FKMTime/firmware/src/state.rs

use crate::consts::NVS_SAVED_STATE;
use crate::{
    structs::{BleDisplayDevice, PossibleGroup},
    utils::error_log::ErrorLogEntry,
    utils::signaled_mutex::SignaledMutex,
};
use alloc::{rc::Rc, string::String, vec::Vec};
use embassy_sync::{
    blocking_mutex::raw::{CriticalSectionRawMutex, NoopRawMutex},
    mutex::Mutex,
    signal::Signal,
};
use embassy_time::{Duration, Instant, Timer};
use esp_hal::aes::Aes;
use esp_hal_wifimanager::Nvs;
use serde::{Deserialize, Serialize};

pub static mut SIGN_KEY: u32 = 0;
pub static mut TRUST_SERVER: bool = false;
pub static mut FKM_TOKEN: i32 = 0;
pub static mut SECURE_RFID: bool = false;
pub static mut AUTO_SETUP: bool = false;

pub static mut GROUP_LIMIT: Option<u64> = None;

pub static mut EPOCH_BASE: u64 = 0;
pub static mut SLEEP_STATE: bool = false;
pub static mut DEEPER_SLEEP: bool = false;
pub static mut OTA_STATE: bool = false;

#[cfg(feature = "v4")]
pub static mut BUZZER_VOLUME: u8 = crate::consts::BUZZER_VOLUME_DEFAULT;

#[cfg(feature = "v4")]
#[inline(always)]
pub fn buzzer_volume() -> u8 {
    unsafe { BUZZER_VOLUME }
}

#[cfg(feature = "v4")]
#[inline(always)]
pub fn set_buzzer_volume(volume: u8) {
    unsafe {
        BUZZER_VOLUME = volume;
    }
}

#[inline(always)]
pub fn current_epoch() -> u64 {
    unsafe { EPOCH_BASE + Instant::now().as_secs() }
}

#[inline(always)]
pub fn sleep_state() -> bool {
    unsafe { SLEEP_STATE }
}

#[inline(always)]
pub fn deeper_sleep_state() -> bool {
    unsafe { DEEPER_SLEEP }
}

#[inline(always)]
pub fn ota_state() -> bool {
    unsafe { OTA_STATE }
}

#[derive(Debug, PartialEq, Clone)]
#[allow(dead_code)]
pub enum Scene {
    Update,

    /// Waiting for wifi connection
    WifiConnect,

    /// Connect to wifi to setup
    AutoSetupWait,

    /// Waiting for MDNS
    MdnsWait,

    WaitingForCompetitor,
    GroupSelect,
    CompetitorInfo,
    Inspection,
    Timer,
    Finished,
}

#[derive(Debug, PartialEq, Clone)]
pub enum MenuScene {
    Signing,
    Unsigning,
    BtDisplay,
    ErrorLog,
    #[cfg(feature = "v4")]
    BuzzerVolume,
}

#[derive(Debug, PartialEq, Clone)]
pub enum ErrorLogEntryStage {
    #[cfg(feature = "v4")]
    Qr,
    // Shared stage used on both variants for post-selection detail view.
    Details,
}

impl Scene {
    pub fn can_be_lcd_overwritten(&self) -> bool {
        match self {
            Scene::Update => false,
            Scene::WifiConnect => false,
            Scene::AutoSetupWait => false,
            Scene::MdnsWait => false,
            Scene::WaitingForCompetitor => true,
            Scene::GroupSelect => true,
            Scene::CompetitorInfo => true,
            Scene::Inspection => false,
            Scene::Timer => false,
            Scene::Finished => false,
        }
    }

    pub fn to_index(&self) -> usize {
        match self {
            Scene::Update => 0,
            Scene::WifiConnect => 1,
            Scene::AutoSetupWait => 2,
            Scene::MdnsWait => 3,
            Scene::WaitingForCompetitor => 4,
            Scene::GroupSelect => 5,
            Scene::CompetitorInfo => 6,
            Scene::Inspection => 7,
            Scene::Timer => 8,
            Scene::Finished => 9,
        }
    }

    pub fn can_sleep(&self) -> bool {
        !matches!(
            self,
            Scene::Update | Scene::WifiConnect | Scene::AutoSetupWait
        )
    }
}

impl PartialOrd for Scene {
    fn partial_cmp(&self, other: &Self) -> Option<core::cmp::Ordering> {
        Some(self.to_index().cmp(&other.to_index()))
    }
}

#[cfg(feature = "e2e")]
#[derive(Default)]
pub struct End2End {
    pub buttons_sig: Signal<CriticalSectionRawMutex, (usize, u64)>,
    pub card_scan_sig: Signal<CriticalSectionRawMutex, u128>,
    pub stackmat_sig:
        Signal<CriticalSectionRawMutex, (crate::utils::stackmat::StackmatTimerState, u64)>,
}

#[cfg(feature = "e2e")]
impl End2End {
    pub fn new() -> Self {
        End2End {
            ..Default::default()
        }
    }
}

#[derive(Debug, Clone, PartialEq)]
pub enum BleAction {
    Connect(BleDisplayDevice),
    StartScan,
    Unpair,
}

pub type GlobalState = Rc<GlobalStateInner>;
pub struct GlobalStateInner {
    pub state: SignaledMutex<CriticalSectionRawMutex, SignaledGlobalStateInner>,
    pub timer_signal: Signal<NoopRawMutex, u64>,
    pub timer_stop_signal: Signal<NoopRawMutex, ()>,
    pub bt_display_signal: Signal<NoopRawMutex, u64>,
    pub update_progress: Signal<CriticalSectionRawMutex, u8>,
    pub sign_unsign_progress: Signal<CriticalSectionRawMutex, bool>,
    pub ble_sig: Signal<CriticalSectionRawMutex, BleAction>,
    pub show_battery: Signal<CriticalSectionRawMutex, u8>,
    #[cfg(feature = "v4")]
    pub buzzer_sound_test: Signal<CriticalSectionRawMutex, ()>,

    pub nvs: Nvs,
    pub aes: Mutex<NoopRawMutex, Aes<'static>>,

    #[cfg(feature = "e2e")]
    pub e2e: End2End,
}

impl GlobalStateInner {
    pub fn new(nvs: &Nvs, aes: esp_hal::peripherals::AES<'static>) -> Self {
        Self {
            state: SignaledMutex::new(SignaledGlobalStateInner::new()),
            timer_signal: Signal::new(),
            timer_stop_signal: Signal::new(),
            bt_display_signal: Signal::new(),
            update_progress: Signal::new(),
            sign_unsign_progress: Signal::new(),
            ble_sig: Signal::new(),
            show_battery: Signal::new(),
            #[cfg(feature = "v4")]
            buzzer_sound_test: Signal::new(),

            nvs: nvs.clone(),
            aes: Mutex::new(Aes::new(aes)),

            #[cfg(feature = "e2e")]
            e2e: End2End::new(),
        }
    }
}

#[derive(Debug, Clone)]
pub struct SignaledGlobalStateInner {
    pub scene: Scene,
    pub menu_scene: Option<MenuScene>,

    pub inspection_start: Option<Instant>,
    pub inspection_end: Option<Instant>,
    pub solve_time: Option<u64>,
    pub penalty: Option<i8>,
    pub session_id: Option<String>,
    pub time_confirmed: bool,
    pub solve_group: Option<PossibleGroup>,

    pub error_text: Option<String>,

    pub possible_groups: Vec<PossibleGroup>,
    pub group_selected_idx: usize,

    pub selected_config_menu: Option<usize>,
    pub error_log_entries: Vec<ErrorLogEntry>,
    pub selected_error_log_item: usize,
    pub selected_error_log_entry: Option<usize>,
    pub error_log_entry_stage: Option<ErrorLogEntryStage>,
    pub error_log_details_scroll: usize,

    pub discovered_bluetooth_devices: Vec<BleDisplayDevice>,
    pub selected_bluetooth_item: usize,

    pub sound_enabled: bool,
    pub device_added: Option<bool>,
    pub server_connected: Option<bool>,
    pub wifi_connected: Option<bool>,
    pub stackmat_connected: Option<bool>,

    pub current_competitor: Option<u64>,
    pub current_judge: Option<u64>,
    pub competitor_display: Option<String>,

    pub delegate_used: bool,
    pub delegate_hold: Option<u8>,

    #[cfg(feature = "v4")]
    pub battery_status: (u8, bool),

    #[cfg(feature = "bat_dev_lcd")]
    pub current_bat_read: Option<f32>,

    #[cfg(feature = "bat_dev_lcd")]
    pub avg_bat_read: Option<f32>,

    pub custom_message: Option<(String, String)>,
}

#[derive(Debug, Clone, Serialize, Deserialize)]
pub struct SavedGlobalState {
    pub inspection_time: Option<u64>,
    pub solve_time: u64,
    pub penalty: i8,
    pub session_id: String,
    pub current_competitor: u64,
    pub solve_epoch: u64,
    pub solve_group: PossibleGroup,
}

impl SignaledGlobalStateInner {
    pub fn new() -> Self {
        Self {
            scene: Scene::WifiConnect,
            menu_scene: None,

            inspection_start: None,
            inspection_end: None,
            solve_time: None,
            penalty: None,
            session_id: None,
            time_confirmed: false,
            solve_group: None,

            error_text: None,
            possible_groups: Vec::new(),
            group_selected_idx: 0,
            selected_config_menu: None,
            error_log_entries: Vec::new(),
            selected_error_log_item: 0,
            selected_error_log_entry: None,
            error_log_entry_stage: None,
            error_log_details_scroll: 0,
            selected_bluetooth_item: 0,
            discovered_bluetooth_devices: Vec::new(),

            sound_enabled: true,
            device_added: None,
            server_connected: None,
            wifi_connected: None,
            stackmat_connected: None,
            current_competitor: None,
            current_judge: None,
            competitor_display: None,

            delegate_used: false,
            delegate_hold: None,

            #[cfg(feature = "v4")]
            battery_status: (0, false),

            #[cfg(feature = "bat_dev_lcd")]
            current_bat_read: None,

            #[cfg(feature = "bat_dev_lcd")]
            avg_bat_read: None,

            custom_message: None,
        }
    }

    pub fn should_skip_other_actions(&self) -> bool {
        if self.error_text.is_some() {
            return true;
        }

        if self.scene.can_be_lcd_overwritten() {
            if self.server_connected == Some(false) {
                return true;
            }

            if self.stackmat_connected == Some(false) {
                return true;
            }
        }

        if self.scene <= Scene::MdnsWait {
            return true;
        }

        false
    }

    pub async fn reset_solve_state(&mut self, save_nvs: Option<&Nvs>) {
        unsafe {
            GROUP_LIMIT = None;
        }
        self.solve_time = None;
        self.penalty = None;
        self.inspection_start = None;
        self.inspection_end = None;
        self.current_competitor = None;
        self.current_judge = None;
        self.competitor_display = None;
        self.session_id = None;
        self.time_confirmed = false;
        self.scene = Scene::WaitingForCompetitor;
        self.delegate_used = false;
        self.inspection_start = None;
        self.inspection_end = None;
        self.solve_group = None;
        self.possible_groups.clear();
        self.group_selected_idx = 0;

        if let Some(nvs) = save_nvs {
            SavedGlobalState::clear_saved_global_state(nvs).await;
        }

        crate::translations::restore_default_locale();
    }

    #[allow(dead_code)]
    pub async fn hard_state_reset(&mut self) {
        unsafe {
            GROUP_LIMIT = None;
        }
        self.scene = Scene::WaitingForCompetitor;
        self.inspection_start = None;
        self.inspection_end = None;
        self.solve_time = None;
        self.penalty = None;
        self.session_id = None;
        self.time_confirmed = false;
        self.solve_group = None;
        self.error_text = None;
        self.possible_groups.clear();
        self.group_selected_idx = 0;
        self.current_competitor = None;
        self.current_judge = None;
        self.competitor_display = None;
        self.delegate_used = false;
        self.delegate_hold = None;
        self.custom_message = None;
    }

    pub fn to_saved_global_state(&self) -> Option<SavedGlobalState> {
        log::debug!("TO_SAVED_STATE: {self:?}");

        Some(SavedGlobalState {
            session_id: self.session_id.clone()?,
            current_competitor: self.current_competitor?,
            penalty: self.penalty.unwrap_or(0),
            solve_time: self.solve_time?,
            inspection_time: self.inspection_end.map(|e| {
                (e.saturating_duration_since(self.inspection_start.unwrap_or(Instant::now())))
                    .as_millis()
            }),
            solve_epoch: current_epoch(),
            solve_group: self.solve_group.clone()?,
        })
    }

    pub fn parse_saved_state(&mut self, saved: SavedGlobalState) {
        log::warn!("Parsed saved state: {saved:?}");

        self.session_id = Some(saved.session_id);
        self.penalty = Some(saved.penalty);
        self.solve_time = Some(saved.solve_time);
        self.current_competitor = Some(saved.current_competitor);
        self.solve_group = Some(saved.solve_group);

        if let Some(inspection_time) = saved.inspection_time {
            let now = Instant::now();
            self.inspection_end = now.checked_add(Duration::from_millis(inspection_time));
            self.inspection_start = Some(now);
        }

        if saved.solve_time > 0 {
            self.scene = Scene::Finished;
        }
    }

    pub fn use_inspection(&self) -> bool {
        match self.solve_group.as_ref().map(|r| r.use_inspection) {
            Some(true) | None => true,
            Some(false) => false,
        }
    }

    #[cfg(feature = "e2e")]
    pub fn snapshot_data(&self) -> crate::structs::SnapshotData {
        let inspection_time = self
            .inspection_end
            .zip(self.inspection_start)
            .map(|(end, start)| (end - start).as_millis());

        crate::structs::SnapshotData {
            scene: self.scene.to_index(),
            inspection_time,
            penalty: self.penalty,
            solve_time: self.solve_time,
            current_judge: self.current_judge,
            current_competitor: self.current_competitor,
            group_selected_idx: self.group_selected_idx,
            time_confirmed: self.time_confirmed,
            possible_groups: self.possible_groups.len(),
        }
    }
}

#[cfg(not(feature = "e2e"))]
impl SavedGlobalState {
    pub async fn from_nvs(nvs: &Nvs) -> Option<Self> {
        while unsafe { EPOCH_BASE == 0 } {
            Timer::after_millis(5).await;
        }

        let res = nvs.get::<Vec<u8>>(NVS_SAVED_STATE).await.ok()?;
        let res: SavedGlobalState = serde_json::from_slice(&res).ok()?;

        // 6hours
        if current_epoch() - res.solve_epoch > 6 * 60 * 60 {
            log::error!("REMOVE SOLVE: {:?} {:?}", current_epoch(), res.solve_epoch);
            return None;
        }

        Some(res)
    }

    pub async fn to_nvs(&self, nvs: &Nvs) {
        use core::sync::atomic::{AtomicBool, Ordering};
        static SAVED_STATE_WRITE_ERR_LOGGED: AtomicBool = AtomicBool::new(false);

        let res = serde_json::to_vec(&self);
        if let Ok(vec) = res {
            _ = nvs.delete(NVS_SAVED_STATE).await;
            let res = nvs.set(NVS_SAVED_STATE, vec.as_slice()).await;
            if let Err(e) = res {
                log::error!("{e:?} Faile to write to nvs! (SAVED_STATE {})", vec.len());
                if !SAVED_STATE_WRITE_ERR_LOGGED.load(Ordering::Relaxed) {
                    crate::utils::error_log::add_error(
                        crate::utils::error_log::codes::NVS_SAVED_STATE_WRITE_FAILED,
                    )
                    .await;

                    SAVED_STATE_WRITE_ERR_LOGGED.store(true, Ordering::Relaxed);
                }
            }
        }
    }

    pub async fn clear_saved_global_state(nvs: &Nvs) {
        use core::sync::atomic::{AtomicBool, Ordering};
        static SAVED_STATE_DELETE_ERR_LOGGED: AtomicBool = AtomicBool::new(false);

        let res = nvs.delete(NVS_SAVED_STATE).await;
        if let Err(e) = res {
            log::error!("{e:?} Faile to delete nvs key! (SAVED_STATE)",);
            if !SAVED_STATE_DELETE_ERR_LOGGED.load(Ordering::Relaxed) {
                crate::utils::error_log::add_error(
                    crate::utils::error_log::codes::NVS_SAVED_STATE_DELETE_FAILED,
                )
                .await;

                SAVED_STATE_DELETE_ERR_LOGGED.store(true, Ordering::Relaxed);
            }
        }
    }
}

#[cfg(feature = "e2e")]
impl SavedGlobalState {
    pub async fn from_nvs(_nvs: &Nvs) -> Option<Self> {
        None
    }

    pub async fn to_nvs(&self, _nvs: &Nvs) {}

    pub async fn clear_saved_global_state(_nvs: &Nvs) {}
}

impl PartialEq for SignaledGlobalStateInner {
    fn eq(&self, other: &Self) -> bool {
        let result = self.scene == other.scene
            && self.menu_scene == other.menu_scene
            && self.inspection_start == other.inspection_start
            && self.inspection_end == other.inspection_end
            && self.solve_time == other.solve_time
            && self.penalty == other.penalty
            && self.session_id == other.session_id
            && self.time_confirmed == other.time_confirmed
            && self.solve_group == other.solve_group
            && self.error_text == other.error_text
            && self.possible_groups == other.possible_groups
            && self.group_selected_idx == other.group_selected_idx
            && self.selected_config_menu == other.selected_config_menu
            && self.error_log_entries == other.error_log_entries
            && self.selected_error_log_item == other.selected_error_log_item
            && self.selected_error_log_entry == other.selected_error_log_entry
            && self.error_log_entry_stage == other.error_log_entry_stage
            && self.error_log_details_scroll == other.error_log_details_scroll
            && self.discovered_bluetooth_devices == other.discovered_bluetooth_devices
            && self.selected_bluetooth_item == other.selected_bluetooth_item
            && self.device_added == other.device_added
            && self.server_connected == other.server_connected
            && self.wifi_connected == other.wifi_connected
            && self.stackmat_connected == other.stackmat_connected
            && self.current_competitor == other.current_competitor
            && self.current_judge == other.current_judge
            && self.competitor_display == other.competitor_display
            && self.delegate_used == other.delegate_used
            && self.delegate_hold == other.delegate_hold
            // battery_status intentionally excluded (v4 hw)
            && self.custom_message == other.custom_message;

        #[cfg(feature = "bat_dev_lcd")]
        let result = result
            && self.current_bat_read == other.current_bat_read
            && self.avg_bat_read == other.avg_bat_read;

        result
    }
}
