FKMTime/firmware/src/bluetooth.rs

use crate::{
    consts::NVS_BONDING_KEY,
    state::{BleAction, GlobalState, MenuScene},
    structs::BleDisplayDevice,
};
use alloc::{rc::Rc, string::ToString, vec::Vec};
use core::cell::RefCell;
use embassy_futures::select::{Either, select, select3, select4};
use embassy_sync::{
    blocking_mutex::raw::{CriticalSectionRawMutex, NoopRawMutex},
    channel::{Channel, Sender},
    signal::Signal,
};
use embassy_time::{Duration, Timer, with_timeout};
use esp_radio::ble::controller::BleConnector;
use rand_core::OsRng;
use trouble_host::prelude::*;

use core::sync::atomic::{AtomicBool, Ordering};

static BLE_INIT_FAILED_LOGGED: AtomicBool = AtomicBool::new(false);
static BLE_MAC_READ_FAILED_LOGGED: AtomicBool = AtomicBool::new(false);
static BLE_BOND_ADD_LOGGED: AtomicBool = AtomicBool::new(false);
static BLE_SCAN_START_LOGGED: AtomicBool = AtomicBool::new(false);
static BLE_BONDABLE_LOGGED: AtomicBool = AtomicBool::new(false);
static BLE_REQUEST_SECURITY_LOGGED: AtomicBool = AtomicBool::new(false);
static BLE_PAIRING_LOGGED: AtomicBool = AtomicBool::new(false);
static BLE_GATT_CLIENT_LOGGED: AtomicBool = AtomicBool::new(false);
static BLE_SERVICE_NOT_FOUND_LOGGED: AtomicBool = AtomicBool::new(false);
static BLE_CHARACTERISTIC_NOT_FOUND_LOGGED: AtomicBool = AtomicBool::new(false);

#[embassy_executor::task]
pub async fn bluetooth_timer_task(
    bt: esp_hal::peripherals::BT<'static>,
    state: GlobalState,
    sleep_sig: Rc<Signal<CriticalSectionRawMutex, bool>>,
) {
    loop {
        let mut sleep = false;
        embassy_futures::select::select(bluetooth_loop(&bt, &state), async {
            loop {
                if sleep_sig.wait().await {
                    sleep = true;
                    break;
                }
            }
        })
        .await;

        Timer::after_millis(1000).await;
        if sleep {
            loop {
                if !sleep_sig.wait().await {
                    break;
                }
            }
        }
    }
}

async fn bluetooth_loop(bt: &esp_hal::peripherals::BT<'static>, state: &GlobalState) {
    loop {
        let mut bond_info = if let Some(bond_info) = load_bonding_info(&state.nvs).await {
            log::info!("Bond stored.");
            Some(bond_info)
        } else {
            log::info!("No bond stored.");

            let current_menu_scene = state.state.lock().await.menu_scene.clone();
            if current_menu_scene != Some(MenuScene::BtDisplay) {
                loop {
                    let sig = state.ble_sig.wait().await;
                    if let BleAction::StartScan = sig {
                        break;
                    }
                }
            }

            None
        };

        let Ok(connector) = BleConnector::new(
            unsafe { bt.clone_unchecked() },
            esp_radio::ble::Config::default(),
        ) else {
            log::error!("Cannot init ble connector");
            if !BLE_INIT_FAILED_LOGGED.load(Ordering::Relaxed) {
                crate::utils::error_log::add_error(crate::utils::error_log::codes::BLE_INIT_FAILED)
                    .await;

                BLE_INIT_FAILED_LOGGED.store(true, Ordering::Relaxed);
            }
            return;
        };

        let controller: ExternalController<_, 20> = ExternalController::new(connector);

        let Ok(mac_addr): Result<[u8; 6], _> =
            esp_hal::efuse::base_mac_address().as_bytes().try_into()
        else {
            log::error!("Cannot read bluetooth mac addr");
            if !BLE_MAC_READ_FAILED_LOGGED.load(Ordering::Relaxed) {
                crate::utils::error_log::add_error(
                    crate::utils::error_log::codes::BLE_MAC_READ_FAILED,
                )
                .await;

                BLE_MAC_READ_FAILED_LOGGED.store(true, Ordering::Relaxed);
            }
            continue;
        };
        let address: Address = Address::random(mac_addr);
        log::info!("[ble] address = {address:x?}");

        let mut resources: HostResources<DefaultPacketPool, 1, 3> = HostResources::new();
        let stack = trouble_host::new(controller, &mut resources)
            .set_random_address(address)
            .set_random_generator_seed(&mut OsRng);
        let Host {
            central,
            mut runner,
            ..
        } = stack.build();

        let mut central = match bond_info {
            Some(ref bond) => {
                if let Err(e) = stack.add_bond_information(bond.clone()) {
                    log::error!("Add bond information failed! ({e:?})");
                    if !BLE_BOND_ADD_LOGGED.load(Ordering::Relaxed) {
                        crate::utils::error_log::add_error(
                            crate::utils::error_log::codes::BLE_BOND_ADD_FAILED,
                        )
                        .await;

                        BLE_BOND_ADD_LOGGED.store(true, Ordering::Relaxed);
                    }
                    break;
                }
                central
            }
            None => {
                let discovery_channel: Channel<NoopRawMutex, BleDisplayDevice, 10> =
                    embassy_sync::channel::Channel::new();
                let printer = BleDiscovery {
                    seen: RefCell::new(heapless::Deque::new()),
                    sender: discovery_channel.sender(),
                };

                let mut scanner = Scanner::new(central);
                {
                    state
                        .state
                        .lock()
                        .await
                        .discovered_bluetooth_devices
                        .clear();
                }

                let _ = select4(
                    runner.run_with_handler(&printer),
                    async {
                        let config = ScanConfig::default();
                        let mut _session = match scanner.scan(&config).await {
                            Ok(s) => s,
                            Err(e) => {
                                log::error!("Cannot start ble scan! ({e:?})");
                                if !BLE_SCAN_START_LOGGED.load(Ordering::Relaxed) {
                                    crate::utils::error_log::add_error(
                                        crate::utils::error_log::codes::BLE_SCAN_START_FAILED,
                                    )
                                    .await;

                                    BLE_SCAN_START_LOGGED.store(true, Ordering::Relaxed);
                                }
                                return;
                            }
                        };

                        loop {
                            Timer::after_millis(10000).await;
                        }
                    },
                    async {
                        loop {
                            let recv = discovery_channel.receive().await;
                            {
                                let mut state = state.state.lock().await;
                                if state.selected_bluetooth_item
                                    >= state.discovered_bluetooth_devices.len()
                                    && state.selected_bluetooth_item > 0
                                {
                                    state.selected_bluetooth_item += 1;
                                }

                                state.discovered_bluetooth_devices.push(recv);
                            }
                        }
                    },
                    async {
                        loop {
                            Timer::after_millis(200).await;
                            if state.ble_sig.signaled() {
                                break;
                            }
                        }
                    },
                )
                .await;

                scanner.into_inner()
            }
        };

        let display_addr = match bond_info {
            Some(ref bond_info) => bond_info.identity.bd_addr.into_inner(),
            None => loop {
                let sig = state.ble_sig.wait().await;
                if let BleAction::Connect(d) = sig {
                    break d.addr;
                }
            },
        };
        let target: Address = Address::random(display_addr);

        let config = ConnectConfig {
            connect_params: Default::default(),
            scan_config: ScanConfig {
                filter_accept_list: &[(target.kind, &target.addr)],
                ..Default::default()
            },
        };

        log::info!("Scanning for peripheral...");
        let _ = select3(
            runner.run(),
            async {
                loop {
                    let sig = state.ble_sig.wait().await;
                    if let BleAction::Unpair = sig {
                        break;
                    }
                }
            },
            async {
                'outer: loop {
                    log::info!("Connecting to {:?}", target);
                    let conn = match with_timeout(Duration::from_secs(5), central.connect(&config))
                        .await
                    {
                        Ok(Ok(conn)) => conn,
                        Ok(Err(e)) => {
                            log::error!("Failed to connect: {:?}", e);
                            Timer::after(Duration::from_secs(1)).await;
                            continue;
                        }
                        Err(_) => {
                            log::error!("Timeout connecting");
                            Timer::after(Duration::from_secs(1)).await;
                            continue;
                        }
                    };

                    // Allow bonding if a bond isn't already stored
                    if let Err(e) = conn.set_bondable(bond_info.is_none()) {
                        log::error!("Set bondable failed! ({e:?})");
                        if !BLE_BONDABLE_LOGGED.load(Ordering::Relaxed) {
                            crate::utils::error_log::add_error(
                                crate::utils::error_log::codes::BLE_BONDABLE_FAILED,
                            )
                            .await;

                            BLE_BONDABLE_LOGGED.store(true, Ordering::Relaxed);
                        }
                        continue;
                    }
                    {
                        if let Err(e) = conn.request_security() {
                            log::error!("Request security failed ({e:?})");
                            if !BLE_REQUEST_SECURITY_LOGGED.load(Ordering::Relaxed) {
                                crate::utils::error_log::add_error(
                                    crate::utils::error_log::codes::BLE_REQUEST_SECURITY_FAILED,
                                )
                                .await;

                                BLE_REQUEST_SECURITY_LOGGED.store(true, Ordering::Relaxed);
                            }
                            continue;
                        }

                        loop {
                            match conn.next().await {
                                ConnectionEvent::PairingComplete {
                                    security_level,
                                    bond,
                                } => {
                                    log::info!("Pairing complete: {:?}", security_level);

                                    if let Some(bond) = bond {
                                        store_bonding_info(&state.nvs, &bond).await;
                                        bond_info = Some(bond);
                                    }

                                    if !security_level.encrypted() {
                                        _ = state.nvs.delete(NVS_BONDING_KEY).await;
                                        break 'outer;
                                    }

                                    break;
                                }
                                ConnectionEvent::PairingFailed(err) => {
                                    log::error!("Pairing failed: {:?}", err);
                                    if !BLE_PAIRING_LOGGED.load(Ordering::Relaxed) {
                                        crate::utils::error_log::add_error(
                                            crate::utils::error_log::codes::BLE_PAIRING_FAILED,
                                        )
                                        .await;

                                        BLE_PAIRING_LOGGED.store(true, Ordering::Relaxed);
                                    }
                                    break;
                                }
                                ConnectionEvent::Disconnected { reason } => {
                                    log::error!(
                                        "Disconnected1: {:?} ({:x})",
                                        reason,
                                        reason.into_inner()
                                    );
                                    if reason.into_inner() == 0x05
                                    /* || reason.into_inner() == 0x3e */
                                    {
                                        // auth failed
                                        _ = state.nvs.delete(NVS_BONDING_KEY).await;
                                        if let Some(ref bond_info) = bond_info {
                                            _ = stack.remove_bond_information(bond_info.identity);
                                        }
                                        break 'outer;
                                    }
                                    break;
                                }
                                _ => {}
                            }
                        }
                    }

                    let Ok(client) =
                        GattClient::<_, DefaultPacketPool, 10>::new(&stack, &conn).await
                    else {
                        log::error!("Failed to create Gatt client!");
                        if !BLE_GATT_CLIENT_LOGGED.load(Ordering::Relaxed) {
                            crate::utils::error_log::add_error(
                                crate::utils::error_log::codes::BLE_GATT_CLIENT_FAILED,
                            )
                            .await;

                            BLE_GATT_CLIENT_LOGGED.store(true, Ordering::Relaxed);
                        }
                        continue;
                    };

                    let conn_fut = async {
                        loop {
                            if let ConnectionEvent::Disconnected { reason } = conn.next().await {
                                log::info!("Disconnected2: {:?}", reason);
                                break;
                            }
                        }
                    };

                    let write_fut = async {
                        let services = match with_timeout(
                            Duration::from_secs(5),
                            client.services_by_uuid(&Uuid::from(
                                0xa5bad9f2700a4c3db9e2e58ad262d40eu128,
                            )),
                        )
                        .await
                        {
                            Ok(Ok(conn)) => conn,
                            Ok(Err(e)) => {
                                log::error!("Failed to connect: {:?}", e);
                                Timer::after(Duration::from_secs(1)).await;
                                return;
                            }
                            Err(_) => {
                                log::error!("Timeout connecting");
                                Timer::after(Duration::from_secs(1)).await;
                                return;
                            }
                        };

                        let Some(service) = services.first().cloned() else {
                            log::error!("Cannot find ble service!");
                            if !BLE_SERVICE_NOT_FOUND_LOGGED.load(Ordering::Relaxed) {
                                crate::utils::error_log::add_error(
                                    crate::utils::error_log::codes::BLE_SERVICE_NOT_FOUND,
                                )
                                .await;

                                BLE_SERVICE_NOT_FOUND_LOGGED.store(true, Ordering::Relaxed);
                            }
                            return;
                        };

                        let Ok(c) = client
                            .characteristic_by_uuid::<u64>(
                                &service,
                                &Uuid::from(0xa5178cade4e045988053a4a78b9281e2u128),
                            )
                            .await
                        else {
                            log::error!("Cannot find ble characteristic!");
                            if !BLE_CHARACTERISTIC_NOT_FOUND_LOGGED.load(Ordering::Relaxed) {
                                crate::utils::error_log::add_error(
                                    crate::utils::error_log::codes::BLE_CHARACTERISTIC_NOT_FOUND,
                                )
                                .await;

                                BLE_CHARACTERISTIC_NOT_FOUND_LOGGED.store(true, Ordering::Relaxed);
                            }
                            return;
                        };

                        let mut data = [0; 8];
                        loop {
                            let ms = state.bt_display_signal.wait().await;
                            data.copy_from_slice(&ms.to_be_bytes());

                            if !conn.is_connected() {
                                break;
                            }

                            if client
                                .write_characteristic_without_response(&c, &data[..])
                                .await
                                .is_err()
                            {
                                break;
                            }
                        }
                    };

                    let gatt_and_conn_events = select(conn_fut, write_fut);
                    match select(client.task(), gatt_and_conn_events).await {
                        Either::Second(Either::First(_)) => {
                            log::info!("Connection event loop finished (disconnected)");
                        }
                        Either::Second(Either::Second(_)) => {
                            log::info!("GATT operations finished");
                        }
                        _ => {}
                    }
                }
            },
        )
        .await;
    }
}

async fn store_bonding_info(nvs: &esp_hal_wifimanager::Nvs, info: &BondInformation) {
    let mut buf = [0; 32];
    _ = nvs.delete(NVS_BONDING_KEY).await;

    buf[..6].copy_from_slice(info.identity.bd_addr.raw());
    buf[6..22].copy_from_slice(info.ltk.to_le_bytes().as_slice());
    buf[22] = match info.security_level {
        SecurityLevel::NoEncryption => 0,
        SecurityLevel::Encrypted => 1,
        SecurityLevel::EncryptedAuthenticated => 2,
    };

    let res = nvs.set(NVS_BONDING_KEY, buf.as_slice()).await;
    if let Err(e) = res {
        log::error!("NVS Bonding key store failed! ({e:?})");
        crate::utils::error_log::add_error(
            crate::utils::error_log::codes::NVS_BONDING_KEY_WRITE_FAILED,
        )
        .await;
    }
}

async fn load_bonding_info(nvs: &esp_hal_wifimanager::Nvs) -> Option<BondInformation> {
    let Ok(buf) = nvs.get::<Vec<u8>>(NVS_BONDING_KEY).await else {
        return None;
    };

    if buf.len() != 32 {
        return None;
    }

    let bd_addr = BdAddr::new(buf[..6].try_into().unwrap_or_default());
    let security_level = match buf[22] {
        0 => SecurityLevel::NoEncryption,
        1 => SecurityLevel::Encrypted,
        2 => SecurityLevel::EncryptedAuthenticated,
        _ => return None,
    };
    let ltk = LongTermKey::from_le_bytes(buf[6..22].try_into().unwrap_or_default());

    Some(BondInformation {
        identity: Identity { bd_addr, irk: None },
        security_level,
        is_bonded: true,
        ltk,
    })
}

#[allow(dead_code)]
struct BleDiscovery<'a> {
    seen: RefCell<heapless::Deque<BdAddr, 128>>,
    sender: Sender<'a, NoopRawMutex, BleDisplayDevice, 10>,
}

impl EventHandler for BleDiscovery<'_> {
    fn on_adv_reports(&self, mut it: LeAdvReportsIter<'_>) {
        let mut seen = self.seen.borrow_mut();
        while let Some(Ok(report)) = it.next() {
            if !seen.iter().any(|b| b.raw() == report.addr.raw()) {
                if let Some(name) = parse_device_name(report.data)
                    && name.starts_with("FKMD-")
                {
                    log::info!("Disovered FKM Display! [{:?}] ({name})", report.addr);

                    _ = self.sender.try_send(BleDisplayDevice {
                        name: name.to_string(),
                        addr: report.addr.into_inner(),
                    });
                }

                if seen.is_full() {
                    seen.pop_front();
                }
                _ = seen.push_back(report.addr);
            }
        }
    }
}

#[allow(dead_code)]
fn parse_device_name(data: &[u8]) -> Option<&str> {
    let mut i = 0;
    while i < data.len() {
        let len = data[i] as usize;
        if len == 0 || i + len >= data.len() {
            break;
        }

        let ad_type = data[i + 1];
        let ad_data = &data[i + 2..i + 1 + len];

        // 0x09 = Complete Local Name, 0x08 = Shortened Local Name
        if ad_type == 0x09 || ad_type == 0x08 {
            return core::str::from_utf8(ad_data).ok();
        }

        i += 1 + len;
    }
    None
}
