FKMTime/firmware/src/board.rs

use esp_hal::{
    gpio::{AnyPin, Input, InputConfig, Output, Pin, Pull},
    peripherals::{
        ADC1, AES, BT, FLASH, Peripherals, SPI2, SW_INTERRUPT, TIMG0, TIMG1, UART1, WIFI,
    },
    rng::Rng,
    timer::timg::TimerGroup,
};

#[cfg(feature = "v4")]
use crate::utils::shared_i2c::SharedI2C;

#[allow(dead_code)]
pub struct Board {
    // peripherals
    pub timg0: TimerGroup<'static, TIMG0<'static>>,
    pub timg1: TimerGroup<'static, TIMG1<'static>>,
    pub rng: Rng,
    pub uart1: UART1<'static>,
    pub spi2: SPI2<'static>,
    pub adc1: ADC1<'static>,
    pub wifi: WIFI<'static>,
    pub bt: BT<'static>,
    pub spi_dma: esp_hal::peripherals::DMA_CH0<'static>,
    pub aes: AES<'static>,
    pub flash: FLASH<'static>,
    pub sw_interrupt: SW_INTERRUPT<'static>,

    // spi
    #[cfg(feature = "v3")]
    pub miso: AnyPin<'static>,
    #[cfg(feature = "v3")]
    pub mosi: AnyPin<'static>,
    #[cfg(feature = "v3")]
    pub sck: AnyPin<'static>,
    #[cfg(feature = "v3")]
    pub cs: adv_shift_registers::wrappers::ShifterPin,

    #[cfg(feature = "v4")]
    pub display_rst: Output<'static>,
    #[cfg(feature = "v4")]
    pub i2c: SharedI2C,
    #[cfg(feature = "v4")]
    pub buzzer: esp_hal::ledc::channel::Channel<'static, esp_hal::ledc::LowSpeed>,

    pub stackmat_rx: AnyPin<'static>,

    #[cfg(feature = "v4")]
    pub buttons: [Input<'static>; 4],

    #[cfg(all(feature = "v4", feature = "timer-func"))]
    pub pads: (Input<'static>, Input<'static>),

    #[cfg(feature = "v3")]
    pub battery: esp_hal::peripherals::GPIO2<'static>,
    #[cfg(feature = "v3")]
    pub button_input: Input<'static>,

    #[cfg(feature = "v3")]
    pub buttons_shifter: adv_shift_registers::wrappers::ShifterValue,
    #[cfg(feature = "v3")]
    pub lcd: adv_shift_registers::wrappers::ShifterValue,

    // usb pins
    pub usb_dp: AnyPin<'static>,
    pub usb_dm: AnyPin<'static>,
}

#[cfg(feature = "v4")]
impl Board {
    pub fn init(peripherals: Peripherals) -> Board {
        let timg0 = TimerGroup::new(peripherals.TIMG0);
        let timg1 = TimerGroup::new(peripherals.TIMG1);
        let rng = Rng::new();
        let uart1 = peripherals.UART1;
        let spi2 = peripherals.SPI2;
        let spi_dma = peripherals.DMA_CH0;
        let adc1 = peripherals.ADC1;
        let wifi = peripherals.WIFI;
        let bt = peripherals.BT;
        let aes = peripherals.AES;
        let flash = peripherals.FLASH;
        let sw_interrupt = peripherals.SW_INTERRUPT;

        let stackmat_rx = peripherals.GPIO20.degrade();
        let usb_dp = peripherals.GPIO19.degrade();
        let usb_dm = peripherals.GPIO18.degrade();

        let display_rst = Output::new(
            peripherals.GPIO7,
            esp_hal::gpio::Level::Low,
            Default::default(),
        );

        let mut ledc = esp_hal::ledc::Ledc::new(peripherals.LEDC);
        ledc.set_global_slow_clock(esp_hal::ledc::LSGlobalClkSource::APBClk);
        let mut lstimer0 =
            ledc.timer::<esp_hal::ledc::LowSpeed>(esp_hal::ledc::timer::Number::Timer0);
        {
            use esp_hal::ledc::timer::TimerIFace;
            _ = lstimer0.configure(esp_hal::ledc::timer::config::Config {
                duty: esp_hal::ledc::timer::config::Duty::Duty5Bit,
                clock_source: esp_hal::ledc::timer::LSClockSource::APBClk,
                frequency: esp_hal::time::Rate::from_hz(2_500),
            });
        }
        let lstimer0: &'static _ = alloc::boxed::Box::leak(alloc::boxed::Box::new(lstimer0));
        let mut buzzer = ledc.channel::<esp_hal::ledc::LowSpeed>(
            esp_hal::ledc::channel::Number::Channel0,
            peripherals.GPIO4,
        );
        {
            use esp_hal::ledc::channel::ChannelIFace;
            _ = buzzer.configure(esp_hal::ledc::channel::config::Config {
                timer: lstimer0,
                duty_pct: 0,
                drive_mode: esp_hal::gpio::DriveMode::PushPull,
            });
        }

        let b1 = Input::new(
            peripherals.GPIO0,
            InputConfig::default().with_pull(Pull::Down),
        );

        let b2 = Input::new(
            peripherals.GPIO1,
            InputConfig::default().with_pull(Pull::Down),
        );

        let b3 = Input::new(
            peripherals.GPIO2,
            InputConfig::default().with_pull(Pull::Down),
        );

        let b4 = Input::new(
            peripherals.GPIO3,
            InputConfig::default().with_pull(Pull::Down),
        );

        #[cfg(feature = "timer-func")]
        let pad1 = Input::new(
            peripherals.GPIO5,
            InputConfig::default().with_pull(Pull::Down),
        );

        #[cfg(feature = "timer-func")]
        let pad2 = Input::new(
            peripherals.GPIO6,
            InputConfig::default().with_pull(Pull::Down),
        );

        let i2c = esp_hal::i2c::master::I2c::new(
            peripherals.I2C0,
            esp_hal::i2c::master::Config::default()
                .with_frequency(esp_hal::time::Rate::from_khz(400)),
        );

        let i2c = match i2c {
            Ok(i2c) => {
                let i2c = i2c
                    .with_sda(peripherals.GPIO8)
                    .with_scl(peripherals.GPIO9)
                    .into_async();

                SharedI2C::new(Some(i2c))
            }
            Err(_) => SharedI2C::new(None),
        };

        Board {
            timg0,
            timg1,
            rng,
            uart1,
            spi2,
            spi_dma,
            adc1,
            wifi,
            bt,
            aes,
            flash,
            sw_interrupt,

            i2c,

            display_rst,
            buzzer,
            stackmat_rx,
            buttons: [b1, b2, b3, b4],

            #[cfg(feature = "timer-func")]
            pads: (pad1, pad2),

            usb_dp,
            usb_dm,
        }
    }
}

#[cfg(feature = "v3")]
impl Board {
    pub fn init(peripherals: Peripherals) -> Board {
        use embedded_hal::digital::OutputPin;
        use esp_hal::gpio::Level;

        let timg0 = TimerGroup::new(peripherals.TIMG0);
        let timg1 = TimerGroup::new(peripherals.TIMG1);
        let rng = Rng::new();
        let uart1 = peripherals.UART1;
        let spi2 = peripherals.SPI2;
        let spi_dma = peripherals.DMA_CH0;
        let adc1 = peripherals.ADC1;
        let wifi = peripherals.WIFI;
        let bt = peripherals.BT;
        let aes = peripherals.AES;
        let flash = peripherals.FLASH;
        let sw_interrupt = peripherals.SW_INTERRUPT;

        let sck = peripherals.GPIO4.degrade();
        let miso = peripherals.GPIO5.degrade();
        let mosi = peripherals.GPIO6.degrade();
        let battery = peripherals.GPIO2;
        let stackmat_rx = peripherals.GPIO20.degrade();
        let usb_dp = peripherals.GPIO19.degrade();
        let usb_dm = peripherals.GPIO18.degrade();

        let button_input = Input::new(
            peripherals.GPIO3,
            InputConfig::default().with_pull(Pull::Down),
        );

        let shifter_data_pin = Output::new(peripherals.GPIO10, Level::Low, Default::default());
        let shifter_latch_pin = Output::new(peripherals.GPIO1, Level::Low, Default::default());
        let shifter_clk_pin = Output::new(peripherals.GPIO21, Level::Low, Default::default());

        let adv_shift_reg = adv_shift_registers::AdvancedShiftRegister::<2, _>::new(
            shifter_data_pin,
            shifter_clk_pin,
            shifter_latch_pin,
            0,
        );
        let adv_shift_reg = alloc::boxed::Box::new(adv_shift_reg);
        let adv_shift_reg = alloc::boxed::Box::leak(adv_shift_reg);

        let mut backlight = adv_shift_reg.get_pin_mut(1, 1, false);
        _ = backlight.set_high();

        let buttons_shifter = adv_shift_reg.get_shifter_mut(0);
        let lcd = adv_shift_reg.get_shifter_mut(1);

        let mut cs = adv_shift_reg.get_pin_mut(1, 0, true);
        _ = cs.set_high();

        Board {
            timg0,
            timg1,
            rng,
            uart1,
            spi2,
            spi_dma,
            adc1,
            wifi,
            bt,
            aes,
            flash,
            sw_interrupt,

            miso,
            mosi,
            sck,
            cs,

            battery,
            stackmat_rx,
            button_input,

            buttons_shifter,
            lcd,
            usb_dp,
            usb_dm,
        }
    }
}
