FKMTime/firmware/src/utils/buttons.rs

use crate::{buttons::HandlersDerive, state::GlobalState};
use alloc::vec::Vec;
use embassy_time::{Instant, Timer};
use esp_hal::gpio::Input;

#[cfg(feature = "v3")]
use crate::consts::BUTTON_DEBOUNCE_MS;

#[allow(dead_code)]
#[derive(Debug, PartialEq, Clone)]
pub enum ButtonTrigger {
    Down,
    Up,
    HoldOnce(u64),
    HoldTimed(u64, u64),
    Hold,
}

#[allow(dead_code)]
#[derive(Debug, PartialEq)]
pub enum Button {
    First,
    Second,
    Third,
    Fourth,
    Unknown,
}

impl From<u8> for Button {
    fn from(value: u8) -> Self {
        match value {
            0b00000001 => Self::First,
            0b00000010 => Self::Second,
            0b00000100 => Self::Third,
            0b00001000 => Self::Fourth,
            _ => Self::Unknown,
        }
    }
}

pub struct ButtonHandler {
    button: Button,
    handlers: Vec<(ButtonTrigger, bool, HandlersDerive)>,
}

pub struct ButtonsHandler {
    default_handler: Option<HandlersDerive>,

    handlers: Vec<ButtonHandler>,
    press_time: Instant,
    last_hold_execute: Instant,
    current_handler_down: Option<usize>,
}

impl ButtonsHandler {
    pub fn new(default_handler: Option<HandlersDerive>) -> Self {
        Self {
            default_handler,

            handlers: Vec::new(),
            press_time: Instant::now(),
            last_hold_execute: Instant::now(),
            current_handler_down: None,
        }
    }

    pub async fn run(
        &mut self,
        state: &GlobalState,
        #[cfg(feature = "v4")] button_inputs: &[Input<'static>],
        #[cfg(feature = "v3")] button_input: &Input<'static>,
        #[cfg(feature = "v3")] button_reg: &adv_shift_registers::wrappers::ShifterValue,
    ) {
        let mut old_val = 0u8;
        // Pending sample while waiting for v3 debounce stability.
        #[cfg(feature = "v3")]
        let mut debounce: Option<(u8, Instant)> = None;

        #[cfg(feature = "e2e")]
        let mut e2e_data = (esp_hal::time::Instant::now(), 0, 0);

        #[cfg(feature = "e2e")]
        let mut send_ack = false;

        #[cfg(feature = "qa")]
        let mut last_button_down = None;

        loop {
            let mut out_val = 0u8;

            #[cfg(feature = "e2e")]
            {
                if state.e2e.buttons_sig.signaled() {
                    let (btn_idx, press_ms) = state.e2e.buttons_sig.wait().await;
                    out_val |= 1 << btn_idx;

                    e2e_data.0 = esp_hal::time::Instant::now();
                    e2e_data.1 = press_ms;
                    e2e_data.2 = btn_idx;
                    send_ack = true;

                    log::debug!("[E2E] Button pressed: {btn_idx} for {press_ms}ms");
                } else if (esp_hal::time::Instant::now() - e2e_data.0).as_millis() <= e2e_data.1 {
                    out_val |= 1 << e2e_data.2;
                }
            }

            #[cfg(feature = "v4")]
            {
                for (i, btn) in button_inputs.iter().enumerate().take(4) {
                    if btn.is_high() {
                        out_val |= 1 << i;
                    }
                }
            }

            #[cfg(feature = "v3")]
            {
                let mut val = 0b10000000;
                for i in 0..4 {
                    button_reg.set_value(val);
                    if button_input.is_high() {
                        out_val |= 1 << i;
                    }

                    val >>= 1;
                }
            }

            // v3: only accept an edge after the new mask is stable for
            // BUTTON_DEBOUNCE_MS (filters bounce / scan glitches).
            // v4: keep immediate edges (per-pin pull-downs on GPIO).
            #[cfg(feature = "v3")]
            let edge = if out_val == old_val {
                debounce = None;
                None
            } else {
                match debounce {
                    Some((cand, since)) if cand == out_val => {
                        if since.elapsed().as_millis() >= BUTTON_DEBOUNCE_MS {
                            debounce = None;
                            Some((old_val, out_val))
                        } else {
                            None
                        }
                    }
                    _ => {
                        debounce = Some((out_val, Instant::now()));
                        None
                    }
                }
            };

            #[cfg(not(feature = "v3"))]
            let edge = if old_val != out_val {
                Some((old_val, out_val))
            } else {
                None
            };

            if let Some((prev, next)) = edge {
                if prev == 0 {
                    #[cfg(not(feature = "qa"))]
                    self.button_down(next.into(), state).await;

                    #[cfg(feature = "qa")]
                    {
                        crate::qa::send_qa_resp(crate::qa::QaSignal::ButtonDown(next));
                        last_button_down = Some(next);
                        log::warn!("Button pressed down: {next}");
                    }
                } else {
                    #[cfg(not(feature = "qa"))]
                    self.button_up(state).await;

                    #[cfg(feature = "qa")]
                    {
                        if let Some(button) = last_button_down {
                            crate::qa::send_qa_resp(crate::qa::QaSignal::ButtonUp(button));
                            last_button_down = None;
                            log::warn!("Button pressed up: {button}");
                        }
                    }

                    #[cfg(feature = "e2e")]
                    if send_ack {
                        crate::ws::send_test_ack(&state).await;
                        send_ack = false;
                    }
                }

                old_val = next;
            }

            if old_val != 0 {
                #[cfg(not(feature = "qa"))]
                self.button_hold(state).await;
            }

            Timer::after_millis(5).await;
        }
    }

    pub fn add_handler(&mut self, button: Button, trigger: ButtonTrigger, func: HandlersDerive) {
        let existing_handler = self.handlers.iter_mut().find(|h| h.button == button);
        match existing_handler {
            Some(handler) => handler.handlers.push((trigger, false, func)),
            None => self.handlers.push(ButtonHandler {
                button,
                handlers: alloc::vec![(trigger, false, func)],
            }),
        }
    }

    pub async fn button_down(&mut self, button: Button, state: &GlobalState) {
        self.press_time = Instant::now();
        let mut handler = self
            .handlers
            .iter_mut()
            .enumerate()
            .find(|(_, h)| h.button == button);

        if let Some(ref default_handler) = self.default_handler {
            let res = default_handler
                .execute(&ButtonTrigger::Down, 0, state)
                .await;

            if res == Ok(true) {
                return;
            }
        }

        if let Some((i, handler)) = &mut handler {
            self.current_handler_down = Some(*i);

            for handler in &mut handler.handlers {
                handler.1 = false;

                if handler.0 == ButtonTrigger::Down {
                    let res = handler.2.execute(&handler.0, 0, state).await;
                    if let Err(e) = res {
                        log::error!("buttons_handler:down_err: {e:?}");
                    }

                    if res == Ok(true) {
                        self.current_handler_down = None; // skip other handlers
                        break;
                    }
                }
            }
        }
    }

    pub async fn button_hold(&mut self, state: &GlobalState) {
        let Some(current_handler_down) = self.current_handler_down else {
            return;
        };

        let handler = &mut self.handlers[current_handler_down];
        let hold_time = (Instant::now() - self.press_time).as_millis();

        for (trigger, activated, handler) in &mut handler.handlers {
            match trigger {
                ButtonTrigger::Down => continue,
                ButtonTrigger::Up => continue,
                ButtonTrigger::HoldTimed(offset, gap) => {
                    if hold_time < *offset
                        || (Instant::now() - self.last_hold_execute).as_millis() < *gap
                    {
                        continue;
                    }

                    let res = handler.execute(trigger, hold_time, state).await;
                    if let Err(e) = res {
                        log::error!("buttons_handler:hold_timed_err: {e:?}");
                    }

                    self.last_hold_execute = Instant::now();
                    if res == Ok(true) {
                        self.current_handler_down = None; // skip other handlers
                        break;
                    }
                }
                ButtonTrigger::Hold => {
                    let res = handler.execute(trigger, hold_time, state).await;
                    if let Err(e) = res {
                        log::error!("buttons_handler:hold_err: {e:?}");
                    }

                    if res == Ok(true) {
                        self.current_handler_down = None; // skip other handlers
                        break;
                    }
                }
                ButtonTrigger::HoldOnce(after) => {
                    if hold_time > *after && !*activated {
                        *activated = true;

                        let res = handler.execute(trigger, hold_time, state).await;
                        if let Err(e) = res {
                            log::error!("buttons_handler:hold_once_err: {e:?}");
                        }

                        if res == Ok(true) {
                            self.current_handler_down = None; // skip other handlers
                            break;
                        }
                    }
                }
            }
        }
    }

    pub async fn button_up(&mut self, state: &GlobalState) {
        let Some(current_handler_down) = self.current_handler_down else {
            return;
        };

        let hold_time = (Instant::now() - self.press_time).as_millis();
        if let Some(ref default_handler) = self.default_handler {
            let res = default_handler
                .execute(&ButtonTrigger::Up, hold_time, state)
                .await;

            if res == Ok(true) {
                self.current_handler_down = None;
                return;
            }
        }

        let handler = &self.handlers[current_handler_down];
        let handlers = handler.handlers.iter().filter(|h| h.0 == ButtonTrigger::Up);
        for handler in handlers {
            let res = handler.2.execute(&handler.0, hold_time, state).await;
            if let Err(e) = res {
                log::error!("buttons_handler:up_err: {e:?}");
            }
        }

        self.current_handler_down = None;
    }
}
